stoonoon/hxsMidiSwitchTouch/hxsMidiSwitchTouch.ino

/*
 * MIDI controller for HX stomp
 * 
 * 
 * 
 * Uses :
 * 
 * Arduino Mega
 * Nextion NX4024K032 Enhanced 3.2" 400*240 touchscreen
 * Modified Crybaby wah as expression pedal
 * 8* footswitch
 * 
 * 
 */
