stoonoon/hxsMidiSwitchTouch/01_includes.ino

#include <MIDI.h>  // https://github.com/FortySevenEffects/arduino_midi_library
#include "Nextion.h" // https://github.com/itead/ITEADLIB_Arduino_Nextion
#define BOUNCE_WITH_PROMPT_DETECTION  // activates more responsive debounce method - must be defined before Bounce2 include
#include <Bounce2.h> // https://github.com/thomasfredericks/Bounce2
