stoonoon/hxsMidiSwitchTouch/04_objects.ino

MidiMessage *individualSwitchAction[footSwitchCount][totalPresetPages][individualActionTypeCount];//array to hold pointers for all action types / pages / footswitches
MidiMessage *comboSwitchAction[footSwitchCount][footSwitchCount][totalPresetPages];//array to hold pointers for 2x switch combination press
